dltech/musicBox/firmware/speex_simplified_dec/speex_types.h

/* speex_types.h taken from libogg */
/********************************************************************
 *                                                                  *
 * THIS FILE IS PART OF THE OggVorbis SOFTWARE CODEC SOURCE CODE.   *
 * USE, DISTRIBUTION AND REPRODUCTION OF THIS LIBRARY SOURCE IS     *
 * GOVERNED BY A BSD-STYLE SOURCE LICENSE INCLUDED WITH THIS SOURCE *
 * IN 'COPYING'. PLEASE READ THESE TERMS BEFORE DISTRIBUTING.       *
 *                                                                  *
 * THE OggVorbis SOURCE CODE IS (C) COPYRIGHT 1994-2002             *
 * by the Xiph.Org Foundation http://www.xiph.org/                  *
 *                                                                  *
 ********************************************************************

 function: #ifdef jail to whip a few platforms into the UNIX ideal.
 last mod: $Id: os_types.h 7524 2004-08-11 04:20:36Z conrad $

 ********************************************************************/
/**
   @file speex_types.h
   @brief Speex types
*/
#ifndef _SPEEX_TYPES_H
#define _SPEEX_TYPES_H


typedef short spx_int16_t;
typedef unsigned short spx_uint16_t;
typedef int spx_int32_t;
typedef unsigned int spx_uint32_t;


#endif  /* _SPEEX_TYPES_H */
